jkordek1/FarmingGame/Arduino code/FarmingGameV9/images.h

const unsigned char confirmIcon [] PROGMEM =
{
  0x01, 0xf8, 0x00, 0x07, 0x0e, 0x00, 0x1c, 0x03, 0x80, 0x30, 0x00, 0xc0, 0x20, 0x00, 0x40, 0x60,
  0x00, 0x60, 0x40, 0x00, 0x20, 0xc0, 0x06, 0x30, 0x80, 0x0c, 0x10, 0x84, 0x18, 0x10, 0x86, 0x30,
  0x10, 0x83, 0x60, 0x10, 0xc1, 0xc0, 0x30, 0x40, 0x80, 0x20, 0x60, 0x00, 0x60, 0x20, 0x00, 0x40,
  0x30, 0x00, 0xc0, 0x1c, 0x03, 0x80, 0x07, 0x0e, 0x00, 0x01, 0xf8, 0x00
};

const unsigned char leftArrow [] PROGMEM = {
 0x01, 0xf8, 0x00, 0x07, 0x0e, 0x00, 0x1c, 0x03, 0x80, 0x30, 0x00, 0xc0, 0x20, 0x00, 0x40, 0x60, 
  0x18, 0x60, 0x40, 0x78, 0x20, 0xc0, 0x78, 0x30, 0x80, 0xf8, 0x10, 0x83, 0xf8, 0x10, 0x83, 0xf8, 
  0x10, 0x81, 0xf8, 0x10, 0xc0, 0x78, 0x30, 0x40, 0x78, 0x20, 0x60, 0x18, 0x60, 0x20, 0x10, 0x40, 
  0x30, 0x00, 0xc0, 0x1c, 0x03, 0x80, 0x07, 0x0e, 0x00, 0x01, 0xf8, 0x00
};

const unsigned char rightArrow [] PROGMEM = {
  0x01, 0xf8, 0x00, 0x07, 0x0e, 0x00, 0x1c, 0x03, 0x80, 0x30, 0x00, 0xc0, 0x20, 0x80, 0x40, 0x61, 
  0x80, 0x60, 0x41, 0xe0, 0x20, 0xc1, 0xf0, 0x30, 0x81, 0xf0, 0x10, 0x81, 0xfc, 0x10, 0x81, 0xfc, 
  0x10, 0x81, 0xf8, 0x10, 0xc1, 0xf0, 0x30, 0x41, 0xe0, 0x20, 0x61, 0x80, 0x60, 0x20, 0x80, 0x40, 
  0x30, 0x00, 0xc0, 0x1c, 0x03, 0x80, 0x07, 0x0e, 0x00, 0x01, 0xf8, 0x00
};

// array size is 5342
static const byte sun[] PROGMEM  = {
  0x89, 0x50, 0x4e, 0x47, 0x0d, 0x0a, 0x1a, 0x0a, 0x00, 0x00, 0x00, 0x0d, 0x49, 0x48, 0x44, 0x52,
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
  0xd2, 0x3c, 0xf3, 0x3c, 0xcc, 0x16, 0x7b, 0xf6, 0x3b, 0xa9, 0x2a, 0x81, 0xb0, 0xc2, 0x60, 0x40, 
  0x26, 0x16, 0x57, 0xb2, 0x56, 0x0d, 0x07, 0xfb, 0x38, 0xb8, 0xeb, 0x35, 0xf6, 0x6e, 0x7d, 0x81, 
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
};
